BoujeeEnjinia1701/trunkbelay/cad/drawings/TKB-DWG-001.png

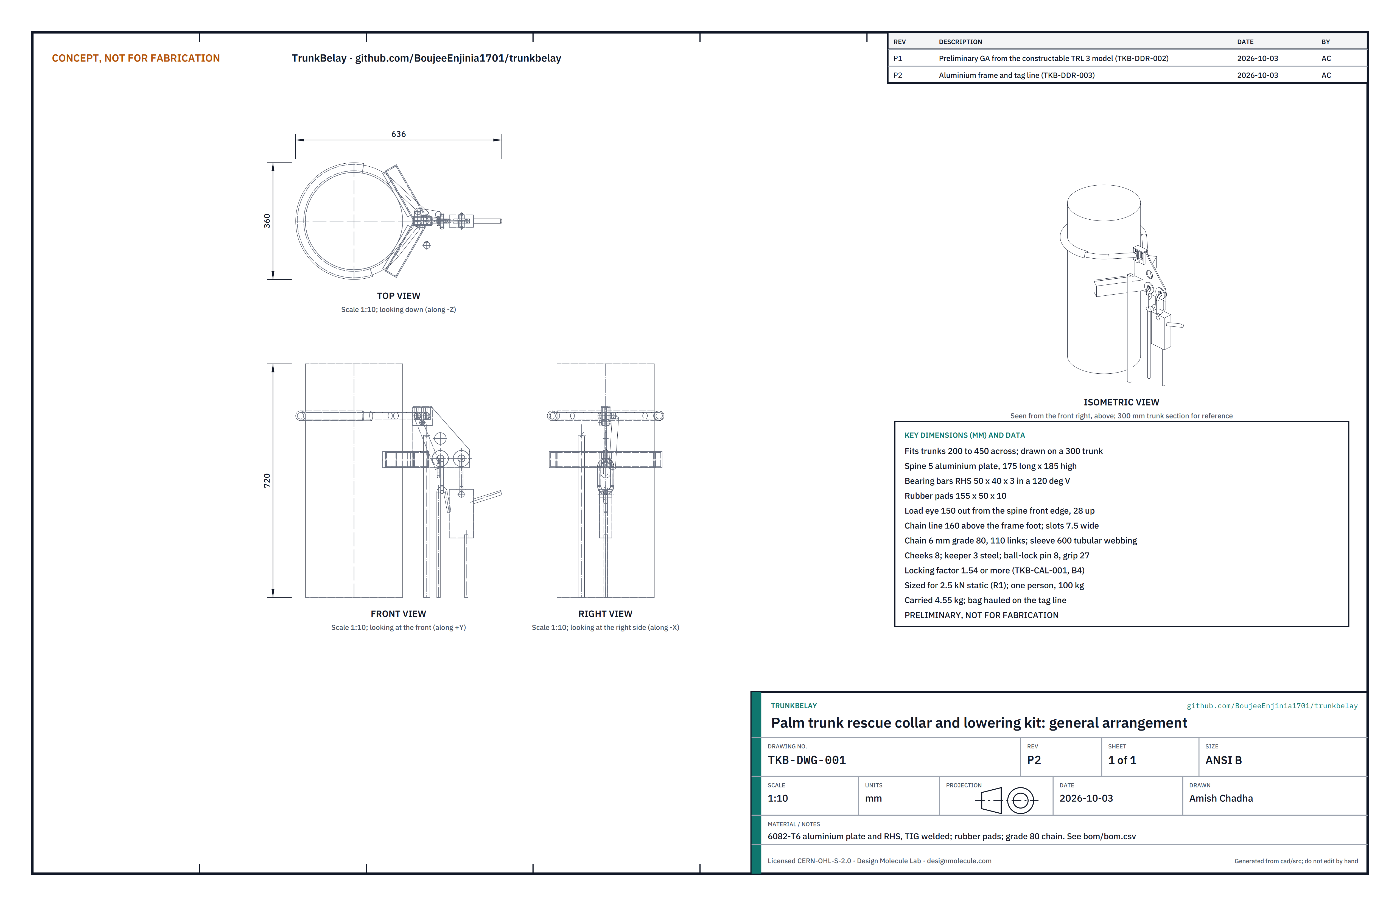
cad/drawings/TKB-DWG-001.png
