BoujeeEnjinia1701/trunkbelay/media/card.png

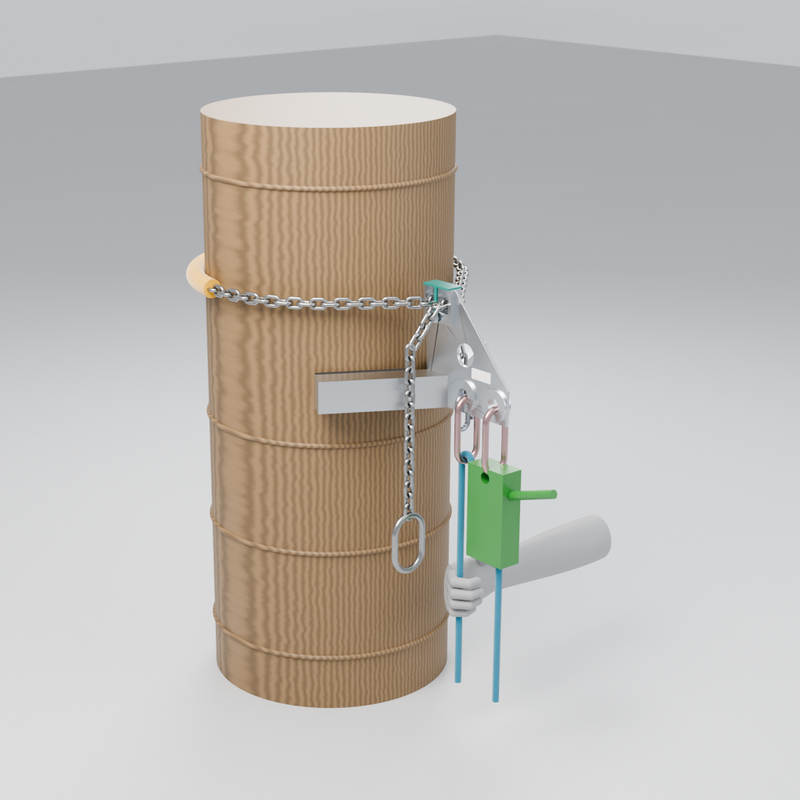
media/card.png
