BoujeeEnjinia1701/trunkbelay/media/render-detail.png

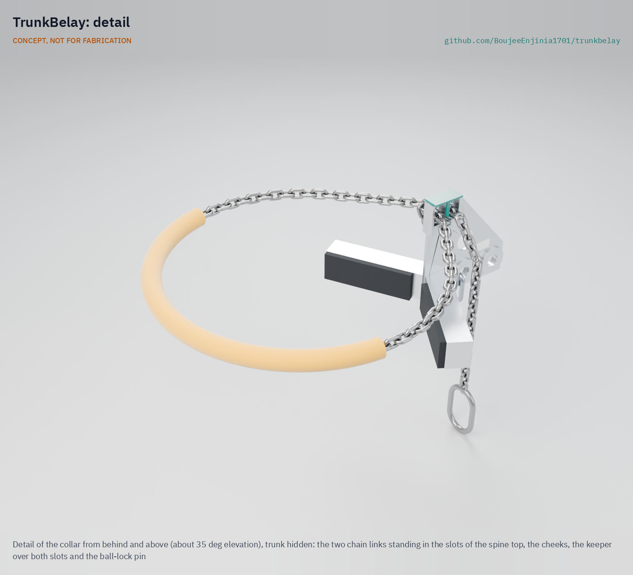
media/render-detail.png
