BoujeeEnjinia1701/trunkbelay/media/render-exploded.png

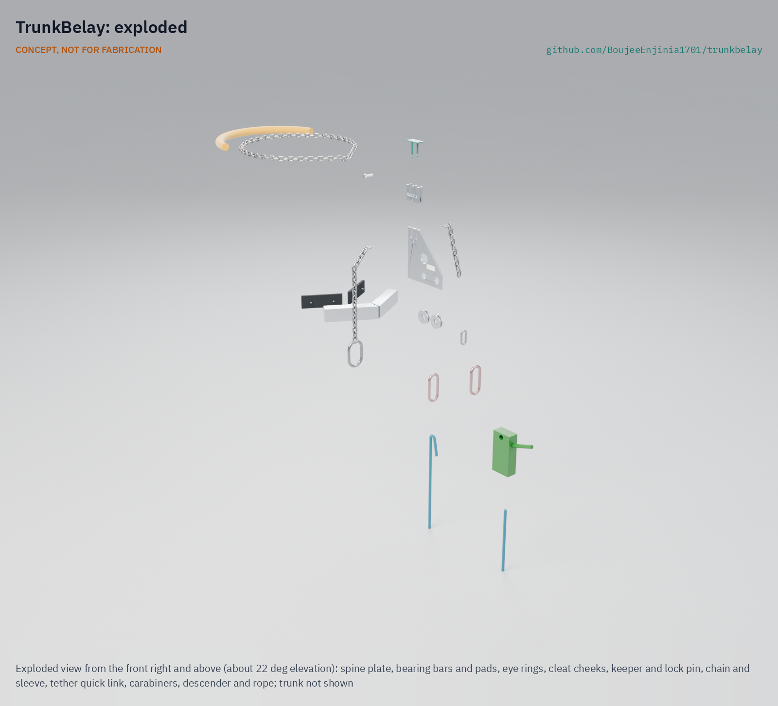
media/render-exploded.png
