BoujeeEnjinia1701/trunkbelay/media/social-preview.png

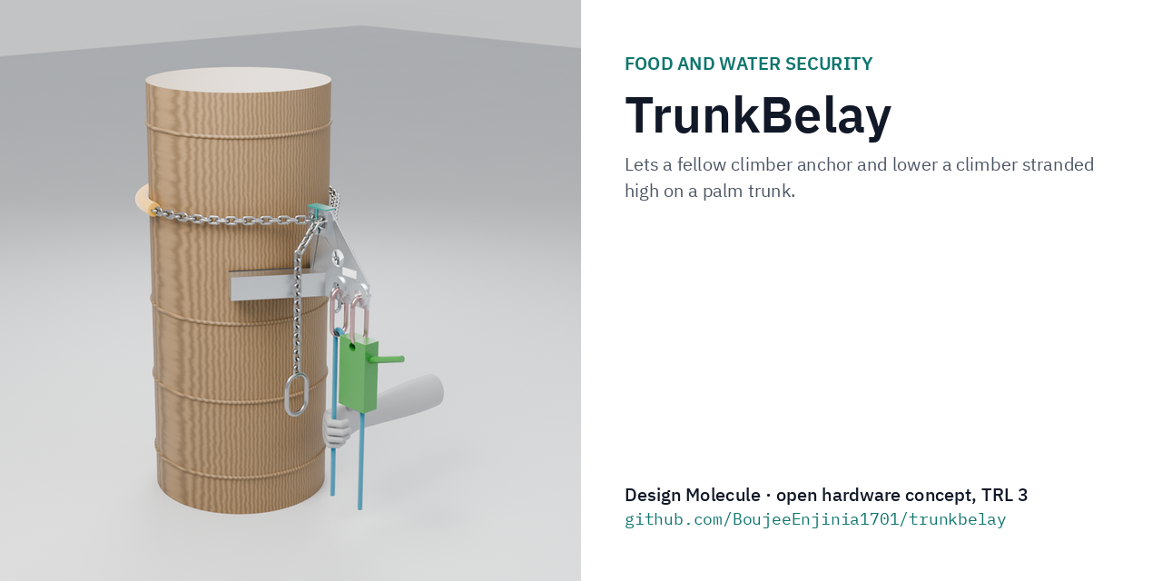
media/social-preview.png
